manhatma/sst/firmware/src/ui/pushbutton.h

#ifndef _PUSHBUTTON_H
#define _PUSHBUTTON_H

#include "pico/time.h"

struct button {
    uint gpio;
    bool state;
    bool enabled;
    alarm_id_t alarm;
    alarm_id_t debounce_alarm;  // New field for debounce timer tracking
    void *user_data;
    void (*onpress)(void *user_data);
    void (*onlongpress)(void *user_data);
};

void create_button(uint gpio, void *user_data, void (*onpress)(void *), void (*onlongpress)(void *));
void disable_button(uint gpio, bool release_only);
void enable_button(uint gpio);

#endif /* _PUSHBUTTON_H */
